markspace/tvprusa/SCADs/functions.scad

// PRUSA Mendel  
// Functions used in many files
// GNU GPL v2
// Josef Průša
// josefprusa@me.com
// prusadjs.cz
// http://www.reprap.org/wiki/Prusa_Mendel
// http://github.com/prusajr/PrusaMendel

module nut( d, h, horizontal = true )
{
	cornerradius = nutcornerdiameter(d)/2;
	cylinder( h = h, r = cornerradius, $fn = 6 );
	if( horizontal )
	{
		for( i = [1 : 6] )
		{
			rotate( [0, 0, 60 * i] ) translate( [-cornerradius - 0.2, 0, 0] ) rotate( [0, 0, -45] ) cube( size = [2, 2, h] );
		}
	}
}

// By nophead
module polyhole( d, h ) 
{
	n = max( round( 2 * d ), 3 );
	rotate( [0, 0, 180] ) cylinder( h = h, r = ( d / 2 ) / cos( 180 / n ), $fn = n );
}

module roundcorner( diameter )
{
	difference()
	{
		cube( size = [diameter, diameter, 99], center = false );
		translate( v = [diameter, diameter, 0] ) cylinder( h = 100, r = diameter, center = true );
	}
}

function nutcornerdiameter(d) = ( d ) / cos( 180 / 6 );
