markspace/tvprusa/SCADs/herringbone-wadebits.scad

// OpenSCAD Herringbone Wade's Gears Script
// (c) 2011, Christopher "ScribbleJ" Jansen
//
// Thanks to Greg Frost for his great "Involute Gears" script.
//
// Licensed under the BSD license.
include <inc/parametric_involute_gear_v5.0.scad> 
include <inc/teardrop.scad> 

// set to 0 for meshed gears, 1 for printing plate with gears flipped and laid flat
printing = 1;

// set to 1 to print each gear.
print_gear_1 = 1;
print_gear_2 = 1;

// OPTIONS COMMON TO BOTH GEARS:
distance_between_axles = 40;
gear_h = 10;
gear_shaft_h = 10;


// GEAR1 (SMALLER GEAR, STEPPER GEAR) OPTIONS:
// It's helpful to choose prime numbers for the gear teeth.
gear1_teeth = 11;
gear1_shaft_d = 5.2;  			// diameter of motor shaft
gear1_shaft_r  = gear1_shaft_d/2;	
// gear1 shaft assumed to fill entire gear.
// gear1 attaches by means of a captive nut and bolt (or actual setscrew)
gear1_setscrew_offset = gear_h / 2;			// Distance from motor on motor shaft.
gear1_setscrew_d         = 3.2;
gear1_setscrew_r          = gear1_setscrew_d/2;
gear1_captive_nut_d = 6.5;
gear1_captive_nut_r  = gear1_captive_nut_d/2;
gear1_captive_nut_h = 2.6;


// GEAR2 (LARGER GEAR, DRIVE SHAFT GEAR) OPTIONS:
gear2_teeth = 45;
gear2_shaft_d = 8.5;
gear2_shaft_r  = gear2_shaft_d/2;
// gear2 has settable outer shaft diameter.
gear2_shaft_outer_d = 20;
gear2_shaft_outer_r  = gear2_shaft_outer_d/2;

// gear2 has a hex bolt set in it, is either a hobbed bolt or has the nifty hobbed gear from MBI on it.
gear2_bolt_hex_d       = 15; //Diameter from point to point (not flat to flat)
gear2_bolt_hex_r        = gear2_bolt_hex_d/2;
// gear2_bolt_sink: How far down the gear shaft the bolt head sits; measured as distance from outer face of gear.
gear2_bolt_sink          = 4;
// gear2's shaft is a bridge above the hex bolt shaft; this creates 1/3bridge_helper_h sized steps at top of shaft to help bridging.  (so bridge_helper_h/3 should be > layer height to have any effect)
bridge_helper_h= 0.35 * 3;

gear2_rim_margin = 0;
gear2_cut_circles  = 5;

// gear2 setscrew option; not likely needed.
gear2_setscrew_offset = 0;
gear2_setscrew_d         = 0;
gear2_setscrew_r          = gear2_setscrew_d/2;
// captive nut for the setscrew
gear2_captive_nut_d = 0;
gear2_captive_nut_r  = gear2_captive_nut_d/2;
gear2_captive_nut_h = 0;

// distance from center of M8 shaft to closest motor screw, so we can position access holes appropriately
motor_mount_access_radius = 22;


// Tolerances for geometry connections.
AT=0.02;
ST=AT*2;
TT=AT/2;


module bridge_helper()
{
	difference()
	{
		translate([0,0,-bridge_helper_h/2])
		cylinder(r=gear2_bolt_hex_r+TT, h=bridge_helper_h+TT,$fn=6,center=true);
		translate([0,0,-bridge_helper_h/2])
		cube([gear2_bolt_hex_d+ST, gear2_shaft_d, bridge_helper_h+AT], center=true);
	}
}



module gearsbyteethanddistance(t1=13,t2=51, d=60, teethtwist=1, which=1)
{
	cp = 360*d/(t1+t2);

	g1twist = 360 * teethtwist / t1;
	g2twist = 360 * teethtwist / t2;

	g1p_d  =  t1 * cp / 180;
	g2p_d  =  t2 * cp / 180;
	g1p_r   = g1p_d/2;
	g2p_r   = g2p_d/2;

	echo(str("Your small ", t1, "-toothed gear will be ", g1p_d, "mm across (plus 1 gear tooth size) (PR=", g1p_r,")"));
	echo(str("Your large ", t2, "-toothed gear will be ", g2p_d, "mm across (plus 1 gear tooth size) (PR=", g2p_r,")"));
	echo(str("Your minimum drive bolt length (to end of gear) is: ", gear2_bolt_sink+bridge_helper_h, "mm and your max is: ", gear_h+gear_shaft_h, "mm."));
	echo(str("Your gear mount axles should be ", d,"mm (", g1p_r+g2p_r,"mm calculated) from each other."));
	if(which == 1)
	{
		// GEAR 1
		difference()
		{
			render()
			union()
			{
				translate([0,0,(gear_h/2) - TT])
					gear(	twist = g1twist, 
						number_of_teeth=t1, 
						circular_pitch=cp, 
						gear_thickness = gear_shaft_h + (gear_h/2)+AT, 
						rim_thickness = (gear_h/2)+AT, 
						rim_width = 0,
						hub_thickness = (gear_h/2)+AT, 
						hub_width = 0,
						bore_diameter=0);
	
				translate([0,0,(gear_h/2) + AT]) rotate([180,0,0]) 
					gear(	twist = -g1twist, 
						number_of_teeth=t1, 
						circular_pitch=cp, 
						gear_thickness = (gear_h/2)+AT, 
						rim_thickness = (gear_h/2)+AT, 
						hub_thickness = (gear_h/2)+AT, 
						bore_diameter=0); 
				translate([0, 0, (gear_h * 1.5) - TT])
					cylinder(r=g1p_r + (cp / 180), h=gear_shaft_h, center=true);
			}
			//DIFFERENCE:
			//shafthole
			translate([0,0,-TT]) 
				cylinder(r=gear1_shaft_r, h=gear_h+gear_shaft_h+ST);

			//setscrew shaft
			translate([0,0,gear_h+gear_shaft_h-gear1_setscrew_offset+0.5]) 
				rotate([0,90,0]) rotate([0,0,22.5])
				cylinder(r=gear1_setscrew_r, h=g1p_d + (cp / 180), $fn=8);

			//setscrew captive nut
			translate([(g1p_r)/2 + 1, 0, gear_h+gear_shaft_h-gear1_setscrew_offset]) 
				union() {
					translate([0, 0, gear1_captive_nut_r])
						cube([gear1_captive_nut_h, gear1_captive_nut_d * cos(30), gear1_setscrew_offset+ST],center=true);
					rotate([0, 90, 0])
						cylinder(h=gear1_captive_nut_h, r=gear1_captive_nut_r, center=true, $fn=6);
				}
			
		
		}
	}
	else
	{
		// GEAR 2
		difference()
		{
			render()
			union()
			{
				translate([0,0,(gear_h/2) - TT])
					gear(	twist = -g2twist, 
						number_of_teeth=t2, 
						circular_pitch=cp, 
						gear_thickness = (gear_h/2)+AT, 
						rim_thickness = (gear_h/2)+AT, 
						rim_width = gear2_rim_margin,
						hub_diameter = gear2_shaft_outer_d,
						hub_thickness = (gear_h/2)+AT, 
						bore_diameter=0); 
	
				translate([0,0,(gear_h/2) + AT]) rotate([180,0,0])
					gear(	twist = g2twist, 
						number_of_teeth=t2, 
						circular_pitch=cp, 
						gear_thickness = (gear_h/2)+AT, 
						rim_thickness = (gear_h/2)+AT, 
						rim_width = gear2_rim_margin,
						hub_diameter = gear2_shaft_outer_d,
						hub_thickness = (gear_h/2)+AT, 
						bore_diameter=0); 
			}
			//DIFFERENCE:
			//shafthole
			translate([0,0,-TT]) 
				cylinder(r=gear2_shaft_r, h=gear_h+gear_shaft_h+ST);

			//setscrew shaft
			translate([0,0,gear_h+gear_shaft_h-gear2_setscrew_offset])
				rotate([0,90,0])
				cylinder(r=gear2_setscrew_r, h=gear2_shaft_outer_d);

			//setscrew captive nut
			translate([(gear2_shaft_outer_d)/2, 0, gear_h+gear_shaft_h-gear2_captive_nut_r-gear2_setscrew_offset]) 
				translate([0,0,(gear2_captive_nut_r+gear2_setscrew_offset)/2])
					#cube([gear2_captive_nut_h, gear2_captive_nut_d, gear2_captive_nut_r+gear2_setscrew_offset+ST],center=true);

			//trim shaft
			difference()
			{
				translate([0,0,gear_h+AT])	cylinder(h=gear_shaft_h+ST, r=g2p_r);
				translate([0,0,gear_h])	cylinder(h=gear_shaft_h, r=gear2_shaft_outer_r);
			}

			//hex bolt shaft
			translate([0,0,-AT]) cylinder(r=gear2_bolt_hex_r, h=gear2_bolt_sink, $fn=6);

			// sunken face
			translate([0, 0, gear_h / 4])
				difference() {
					cylinder(r = g2p_r - (cp / 45), h=gear_h, center=true);
					cylinder(r = gear2_shaft_outer_r, h=gear_h + TT, center=true);
				}

			// motor mount access screw
			for(i = [0:7]) {
//				translate([motor_mount_access_radius * cos((i * 45) + 22.5), motor_mount_access_radius * sin((i * 45) + 22.5), gear_h / 2])
				rotate([0, 0, (45 * i) + 22.5])
					translate([motor_mount_access_radius, 0, gear_h / 2])
					//cylinder(r=3, h=(gear_h * 2), center=true);
					rotate([0, 270, 90])
						teardrop(3, gear_h * 2, 90);
			}

			// weight/plastic reduction and branding
			for (i = [0:7]) {
				rotate([0, 0, 45 * i])
				translate([gear2_shaft_outer_r + (g2p_r / 6) + AT, 0, gear_h / 2])
					rotate([0, 90, 0])
					teardrop(g2p_r / 7, gear_h * 2, 90);
			}
		}

		// hex bolt shaft bridge aid.
		/*
		translate([0, 0, gear2_bolt_sink]) {
			translate ([0,0,])
				bridge_helper();
			translate ([0,0,bridge_helper_h/3])
				rotate([0,0,60]) bridge_helper();
			translate ([0,0,((bridge_helper_h/3)*2)])
				rotate([0,0,-60]) bridge_helper();
		}
		/**/	
	}
	
}


t1 = gear1_teeth;
t2 = gear2_teeth;
cp = 360*distance_between_axles/(t1+t2);
g1p_d  =  t1 * cp / 180;
g2p_d  =  t2 * cp / 180;
g1p_r   = g1p_d/2;
g2p_r   = g2p_d/2;

if (print_gear_1==1){
translate([-10, 45, 0])
	render()
		translate([-g1p_r,0,0]) rotate([0,0,($t*360/gear1_teeth)]) {
			intersection() {
				union() {
					translate([0, 0, 0]) #cylinder(r1=g1p_r, r2=g1p_r + (cp / 180), h=(cp / 180));
					translate([0, 0, (cp / 180) - 0.01]) #cylinder(r=g1p_r + (cp / 180), h=10.02 - (cp / 180) - (cp / 180));
					translate([0, 0, 10 - (cp / 180)]) #cylinder(r2=g1p_r, r1=g1p_r + (cp / 180), h=(cp / 180));
					translate([0, 0, 10]) cylinder(r1=g1p_r, r2=g1p_r + (cp / 180) + 0.1, h=(cp / 180) + 0.2);
					translate([0, 0, 10 + (cp / 180)]) cylinder(r=g1p_r + (cp / 180) + 1, h = 11);
				}
				gearsbyteethanddistance(t1 = gear1_teeth, t2=gear2_teeth, d=distance_between_axles, which=1);
			}
		}
}
if(print_gear_2==1){
translate([0, 0, gear_h * printing]) rotate([180 * printing, 0, 0])
	render()
		translate([g2p_r,0,0])  rotate([0,0,($t*360/gear2_teeth)*-1]) {
			intersection() {
				union() {
					translate([0, 0, 0]) #cylinder(r1=g2p_r, r2=g2p_r + (cp / 180), h=(cp / 180));
					translate([0, 0, (cp / 180) - 0.01]) #cylinder(r=g2p_r + (cp / 180), h=10.02 - (cp / 180) - (cp / 180));
					translate([0, 0, 10 - (cp / 180)]) #cylinder(r2=g2p_r, r1=g2p_r + (cp / 180), h=(cp / 180));
					translate([0, 0, 10]) cylinder(r1=g2p_r, r2=g2p_r + (cp / 180) + 0.1, h=(cp / 180) + 0.2);
				}
				gearsbyteethanddistance(t1 = gear1_teeth, t2=gear2_teeth, d=distance_between_axles, which=2);
			}
		}
}
